beamworld/iWatch-Bilibili-TV-cover/output/render/iWatch_Bilibili-TV_AD.8.png

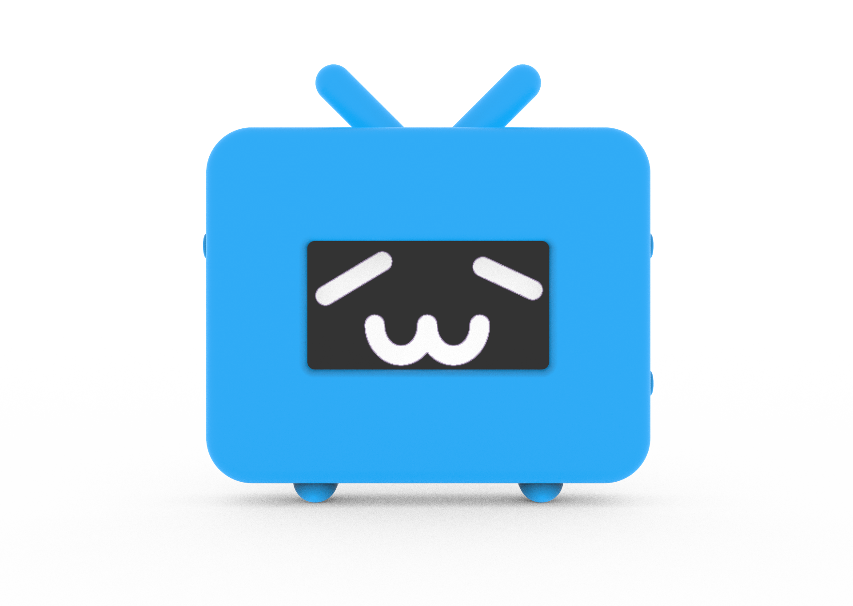
output/render/iWatch_Bilibili-TV_AD.8.png
