beamworld/iWatch-Bilibili-TV-cover/output/render/iWatch_Thin_cover_AD.8.jpg

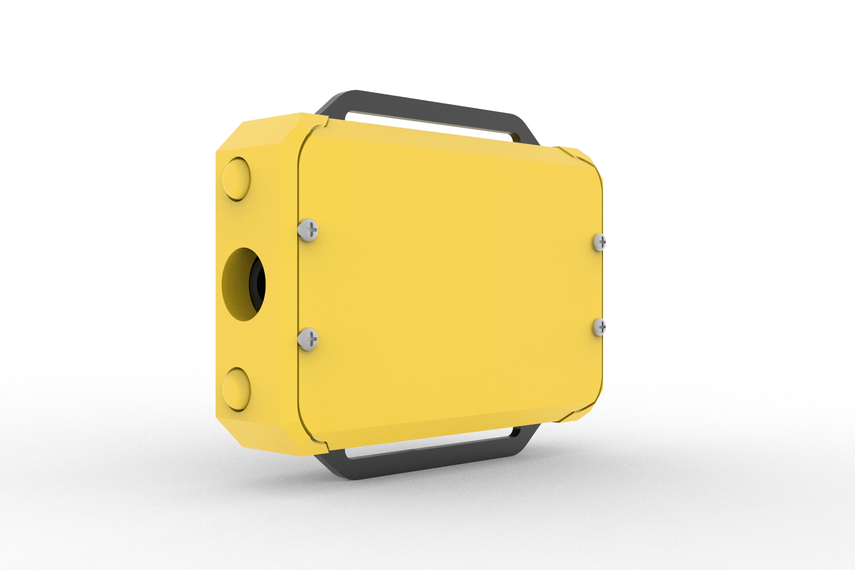
output/render/iWatch_Thin_cover_AD.8.jpg
