beamworld/iWatch-Bilibili-TV-cover/output/render/iWatch_unit_Rev0.9.png

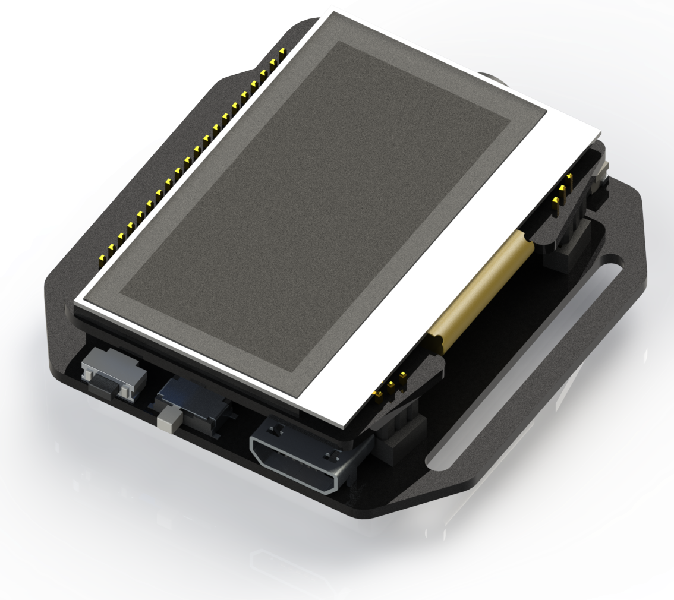
output/render/iWatch_unit_Rev0.9.png
