beamworld/iWatch-Bilibili-TV-cover/component/Beep/Beep_5020_SMT.SLDPRT

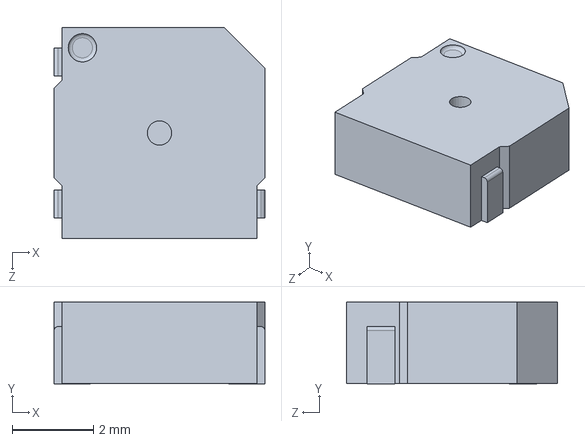
[picture p43: CAD file, 2020-08-19]
component/Beep/Beep_5020_SMT.SLDPRT
5.20 x 2.01 x 5.20 mm
