beamworld/iWatch-Bilibili-TV-cover/component/Button/Button_2x4mm_Side_SMT.SLDPRT

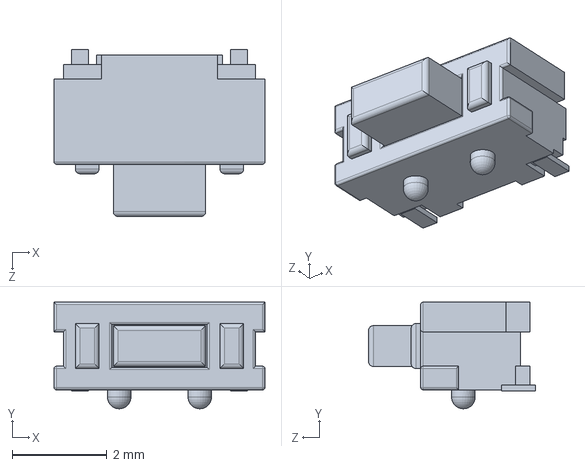
[picture p44: CAD file, 2020-08-19]
component/Button/Button_2x4mm_Side_SMT.SLDPRT
4.45 x 2.25 x 3.52 mm
