beamworld/iWatch-Bilibili-TV-cover/component/Header/Female-header_1.27mm_single_2mm-high.SLDPRT

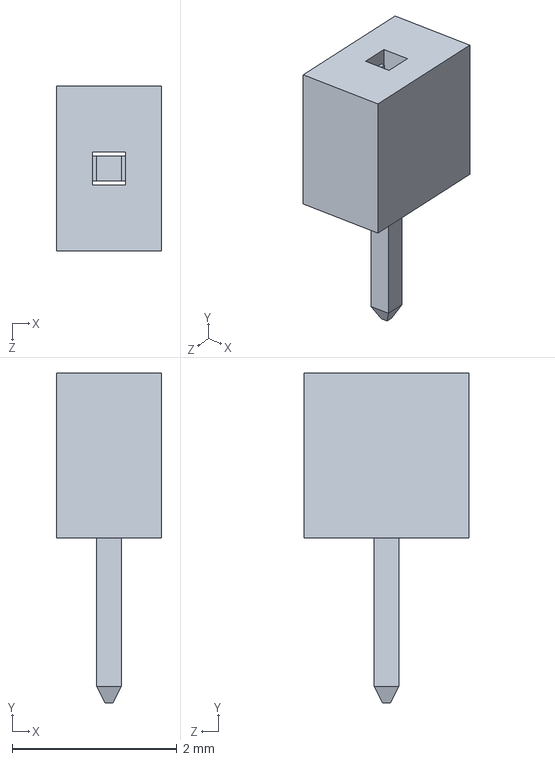
[picture p45: CAD file, 2020-08-19]
component/Header/Female-header_1.27mm_single_2mm-high.SLDPRT
1.27 x 4.00 x 2.00 mm
