beamworld/iWatch-Bilibili-TV-cover/component/IC/SOT23-6/SOT23-6.sldprt

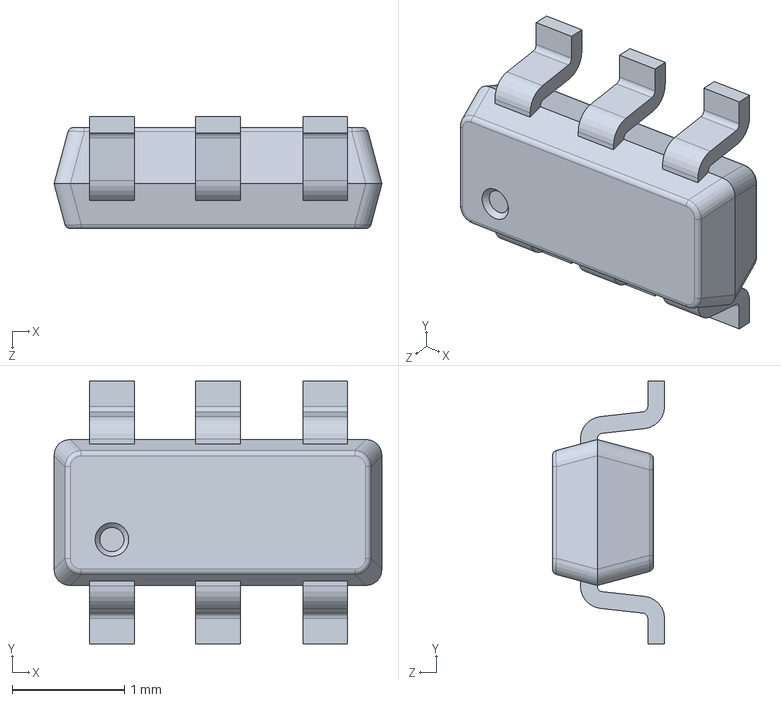
[picture p46: CAD file, 2020-08-19]
component/IC/SOT23-6/SOT23-6.sldprt
2.92 x 2.34 x 1.00 mm
