beamworld/iWatch-Bilibili-TV-cover/component/IC/STC51/STC51.SLDPRT

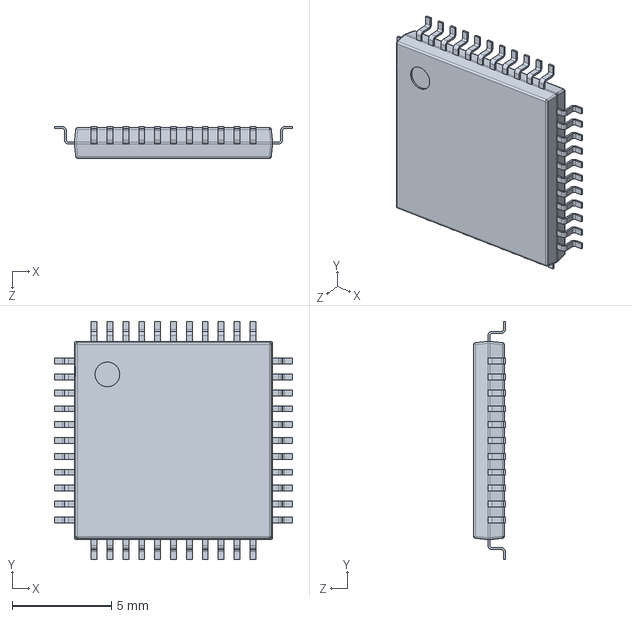
[picture p47: CAD file, 2020-08-19]
component/IC/STC51/STC51.SLDPRT
12.0 x 12.0 x 1.60 mm
