beamworld/iWatch-Bilibili-TV-cover/component/Jack/Phone_jack_PJ327A_5P_SMT.SLDPRT

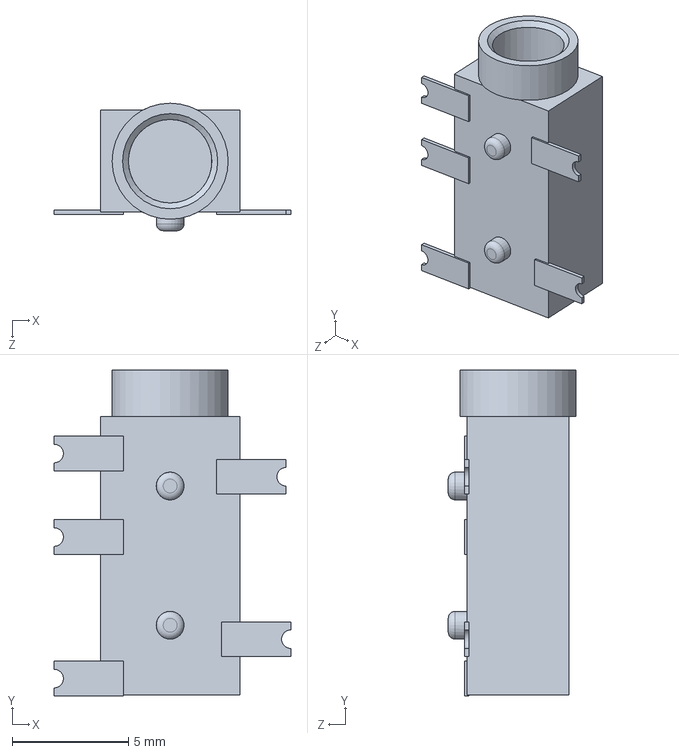
[picture p48: CAD file, 2020-08-19]
component/Jack/Phone_jack_PJ327A_5P_SMT.SLDPRT
10.2 x 14.1 x 5.50 mm
