beamworld/iWatch-Bilibili-TV-cover/component/OLED/1.3inch_OLED.sldprt

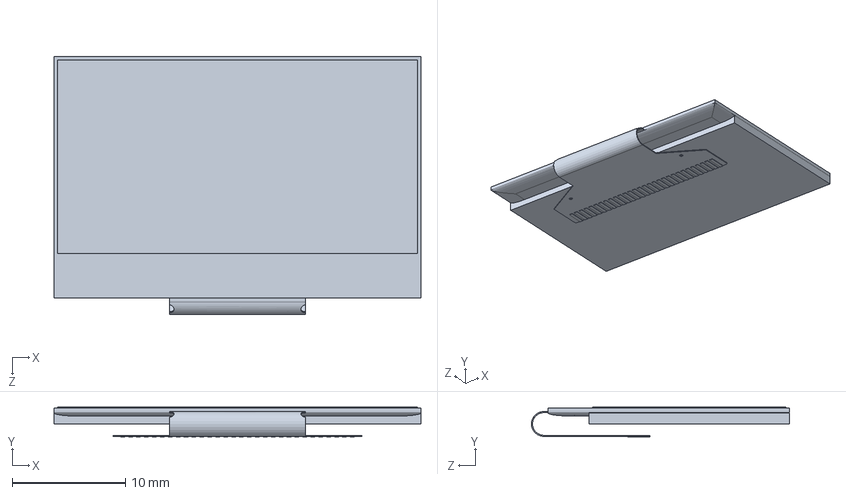
[picture p49: CAD file, 2020-08-19]
component/OLED/1.3inch_OLED.sldprt
32.4 x 2.65 x 22.8 mm
