beamworld/iWatch-Bilibili-TV-cover/component/Switch/Switch_mini_5x3mm_SPDT_Side_SMT.SLDPRT

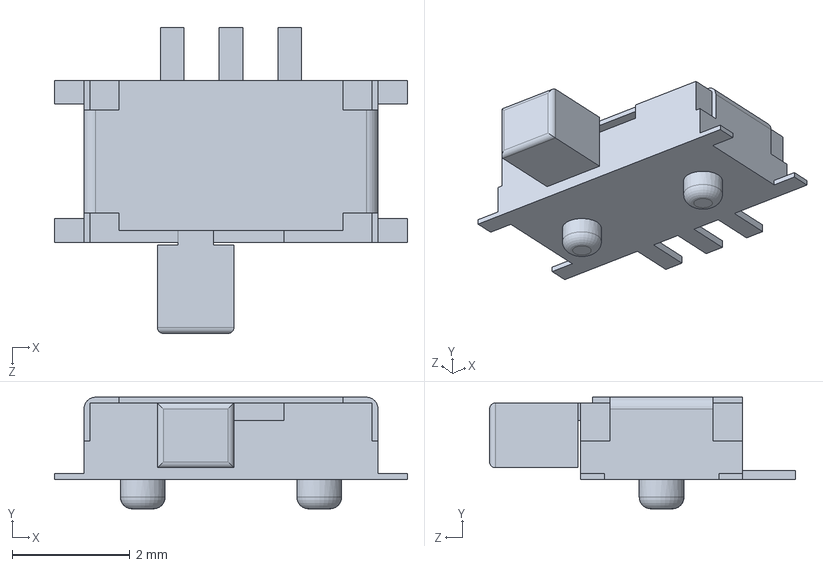
[picture p50: CAD file, 2020-08-19]
component/Switch/Switch_mini_5x3mm_SPDT_Side_SMT.SLDPRT
6.00 x 1.90 x 5.20 mm
