beamworld/iWatch-Bilibili-TV-cover/component/USB/MicroUSB_SMT.sldprt

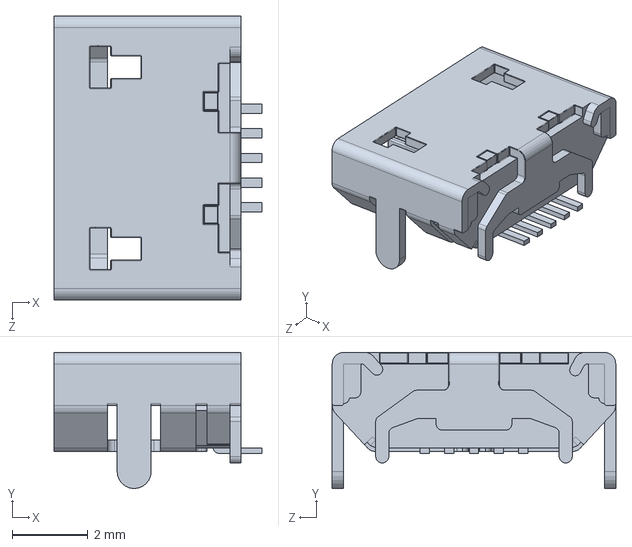
[picture p51: CAD file, 2020-08-19]
component/USB/MicroUSB_SMT.sldprt
5.50 x 3.60 x 7.50 mm
