beamworld/iWatch-Bilibili-TV-cover/output/stl/Bilibili_part1.STL

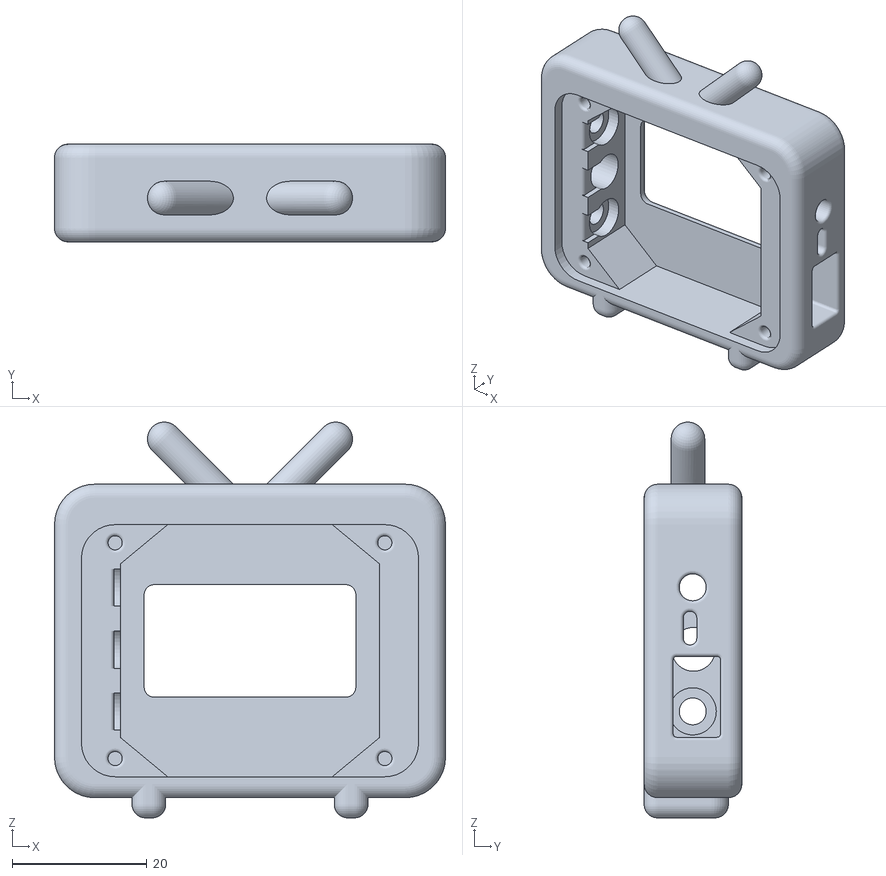
[picture p52: CAD file, 2020-08-21]
output/stl/Bilibili_part1.STL
58.0 x 14.5 x 58.7
