beamworld/iWatch-Bilibili-TV-cover/source/step/iWatch-screen.step

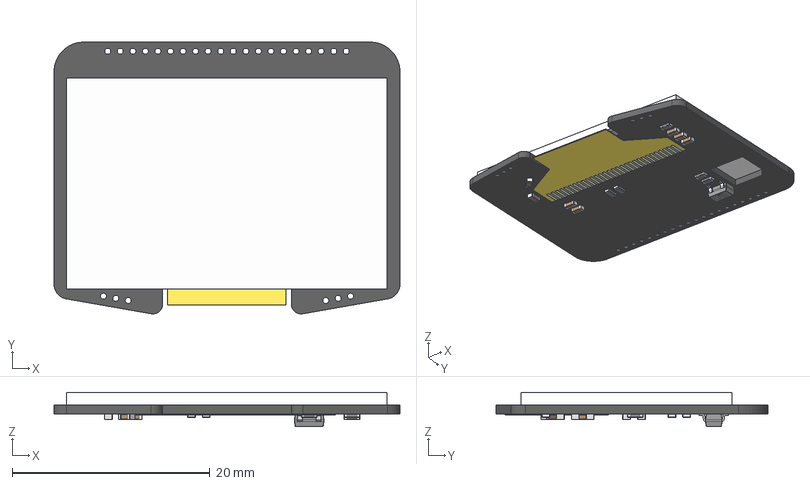
[picture p53: CAD file, 2020-08-19]
source/step/iWatch-screen.step
35.0 x 27.5 x 3.47 mm
Board
RESC1608(0603) x 5
SOT-23
CAPC1608(0603) x 7
Extruded x 35
