beamworld/iWatch-Bilibili-TV-cover/standard_part/M1.2x3.sldprt

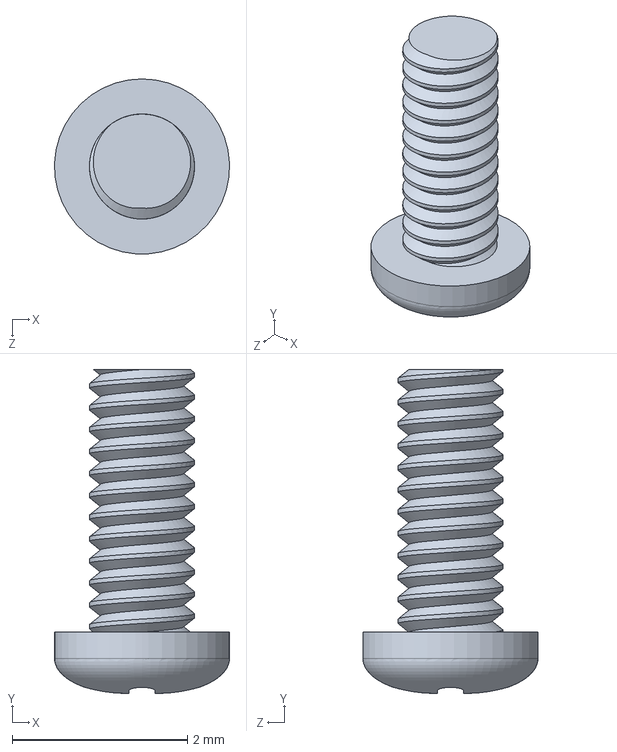
[picture p54: CAD file, 2020-08-20]
standard_part/M1.2x3.sldprt
2.00 x 3.70 x 2.00 mm
