beamworld/iWatch-Bilibili-TV-cover/component/0805/0805_R.sldprt

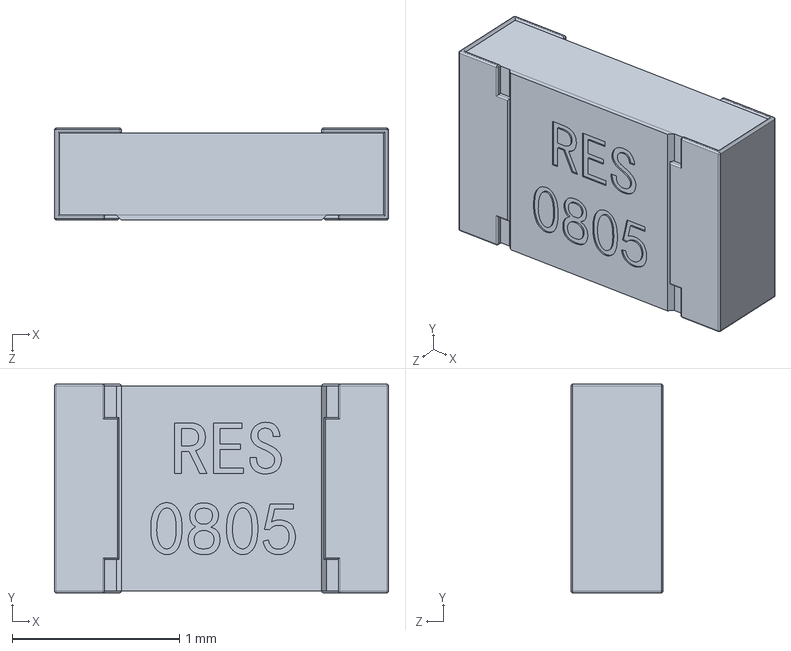
[picture p55: CAD file, 2020-08-19]
component/0805/0805_R.sldprt
2.00 x 1.25 x 0.55 mm
