beamworld/iWatch-Bilibili-TV-cover/component/Battery/Battery_protection_board.SLDPRT

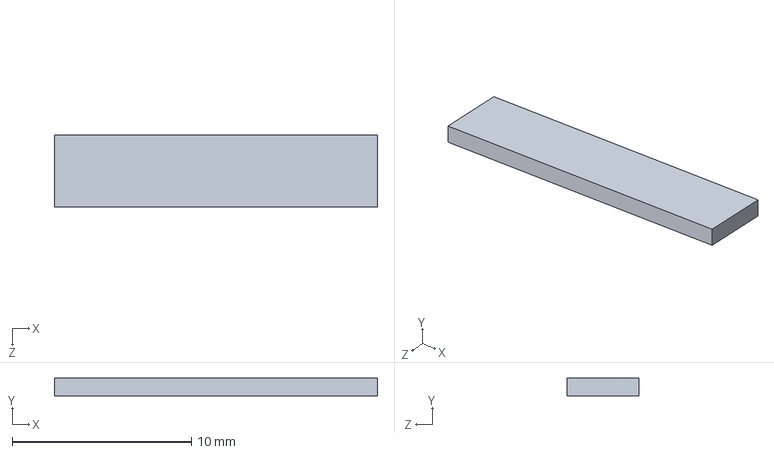
[picture p56: CAD file, 2020-08-19]
component/Battery/Battery_protection_board.SLDPRT
18.0 x 1.00 x 4.00 mm
