beamworld/iWatch-Bilibili-TV-cover/output/stl/Thin_cover_part1.STL

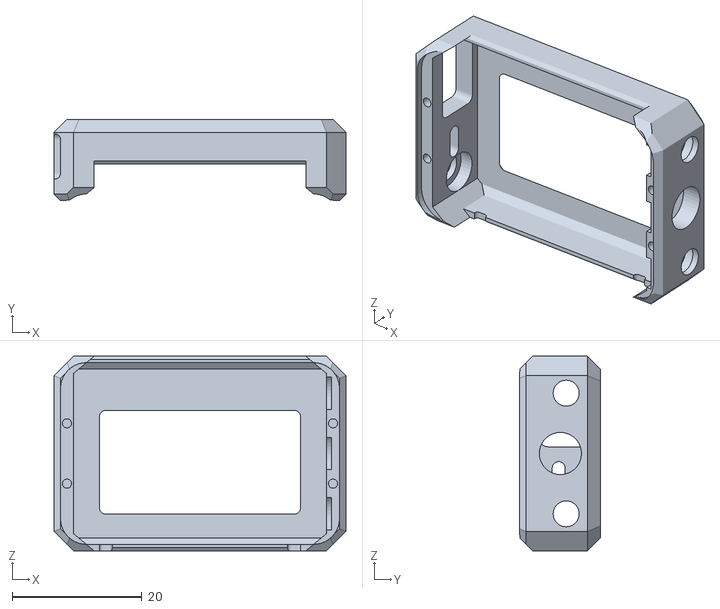
[picture p57: CAD file, 2020-08-21]
output/stl/Thin_cover_part1.STL
45.0 x 12.5 x 30.0
