beamworld/iWatch-Bilibili-TV-cover/component/0805/0805_LED.sldprt

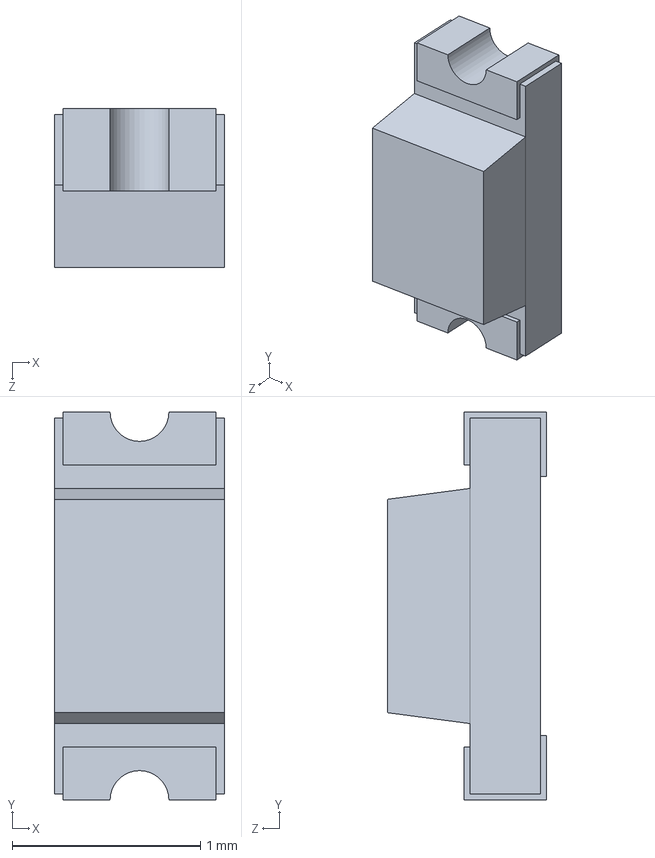
[picture p58: CAD file, 2020-08-19]
component/0805/0805_LED.sldprt
0.906 x 2.06 x 0.844 mm
