beamworld/iWatch-Bilibili-TV-cover/output/stl/Thin_cover_part2_cap.STL

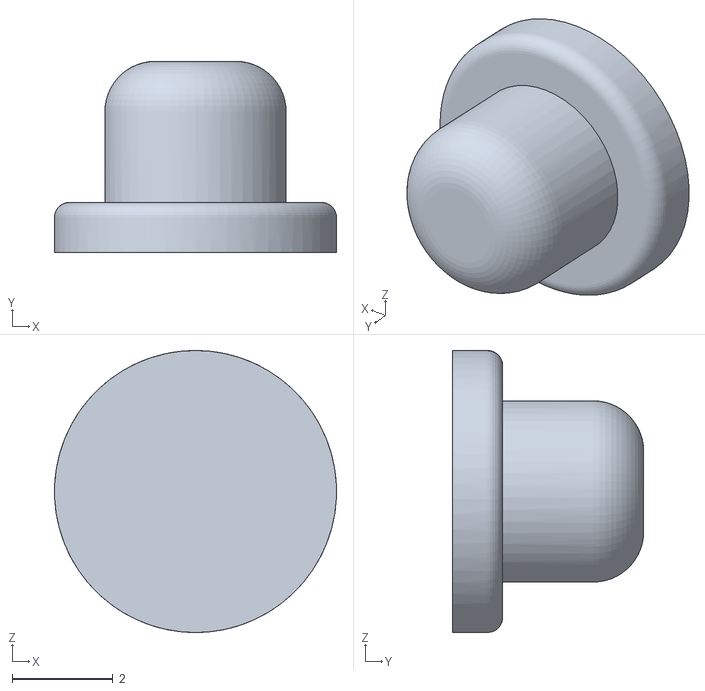
[picture p59: CAD file, 2020-08-21]
output/stl/Thin_cover_part2_cap.STL
5.60 x 3.80 x 5.60
