beamworld/iWatch-Bilibili-TV-cover/output/stl/Thin_cover_part3.STL

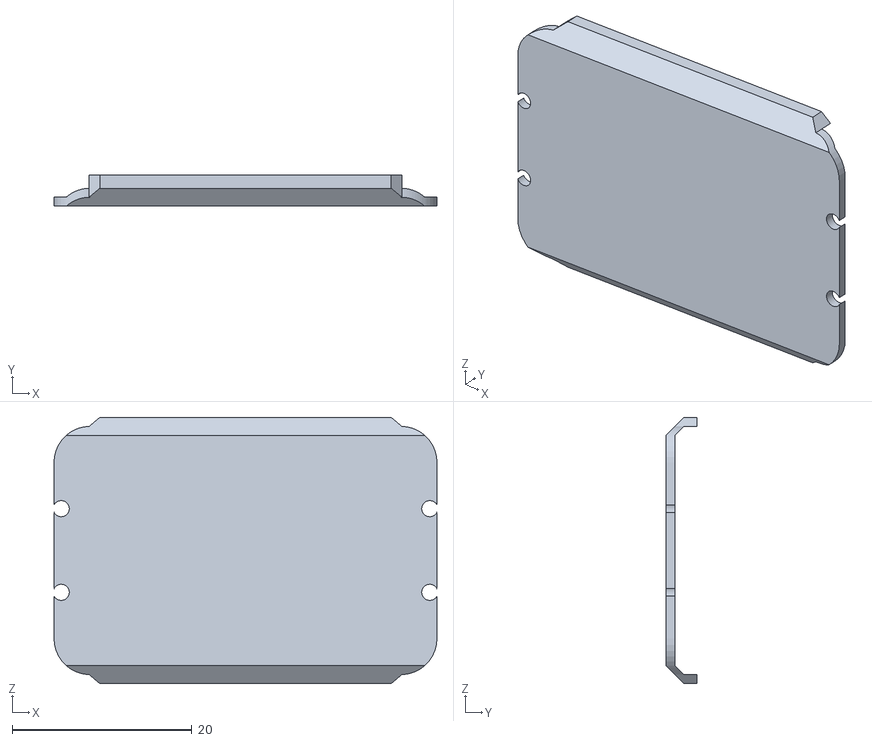
[picture p60: CAD file, 2020-08-20]
output/stl/Thin_cover_part3.STL
42.6 x 3.50 x 29.6
