beamworld/iWatch-Bilibili-TV-cover/component/Battery/0402_R.sldprt

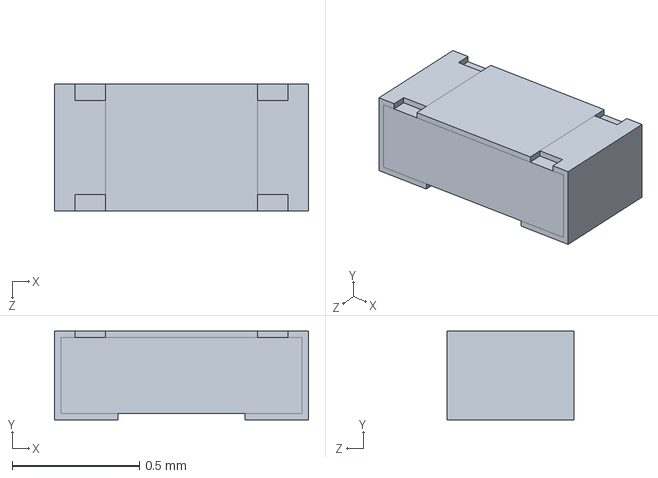
[picture p61: CAD file, 2020-08-19]
component/Battery/0402_R.sldprt
1.00 x 0.35 x 0.5 mm
