beamworld/iWatch-Bilibili-TV-cover/output/stl/Bilibili_part3.STL

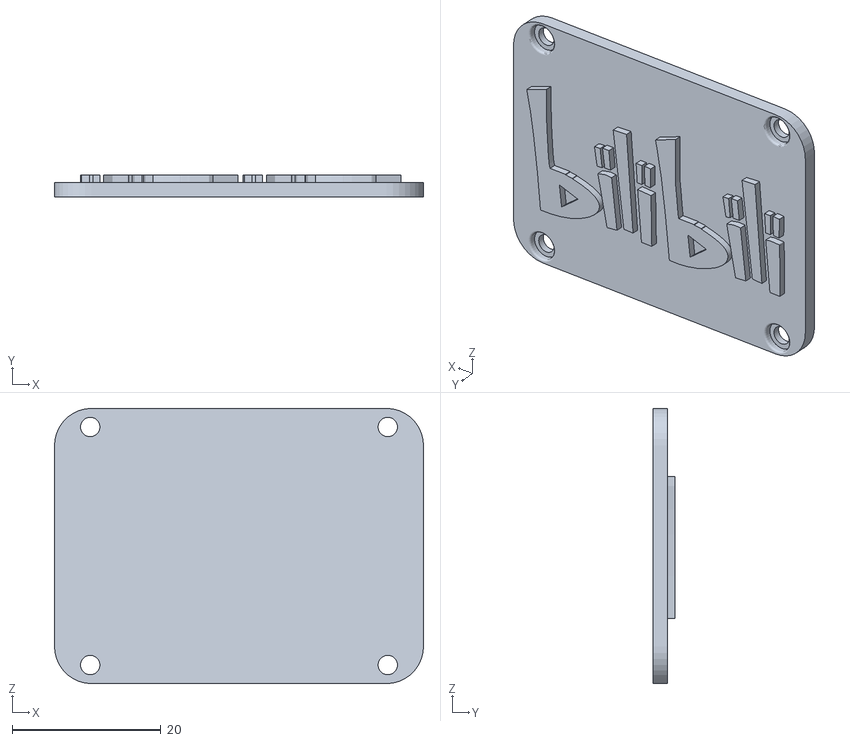
[picture p62: CAD file, 2020-08-20]
output/stl/Bilibili_part3.STL
49.6 x 3.00 x 37.0
