beamworld/iWatch-Bilibili-TV-cover/component/Battery/0201_R.SLDPRT

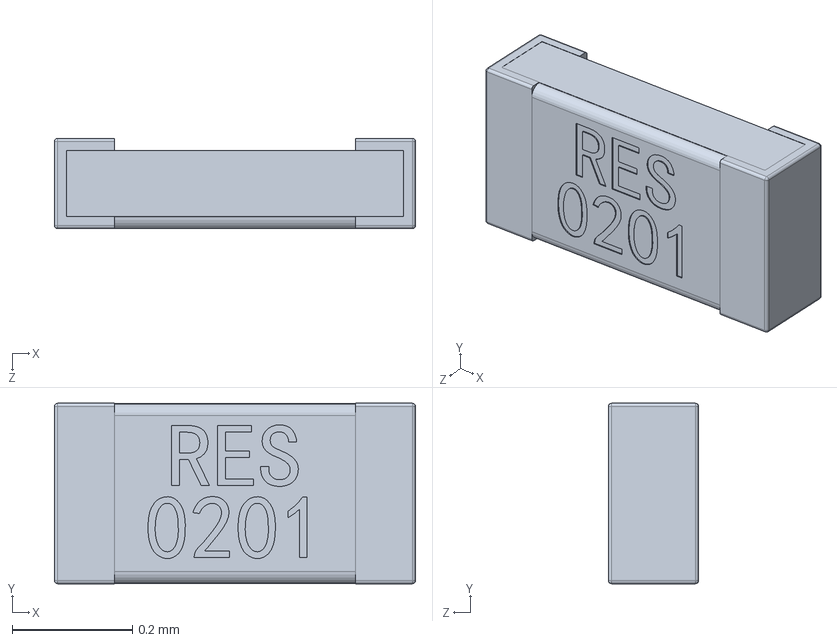
[picture p63: CAD file, 2020-08-19]
component/Battery/0201_R.SLDPRT
0.6 x 0.3 x 0.15 mm
