beamworld/iWatch-Bilibili-TV-cover/component/Header/Male-header_1.27mm_single_2mm-high.SLDPRT

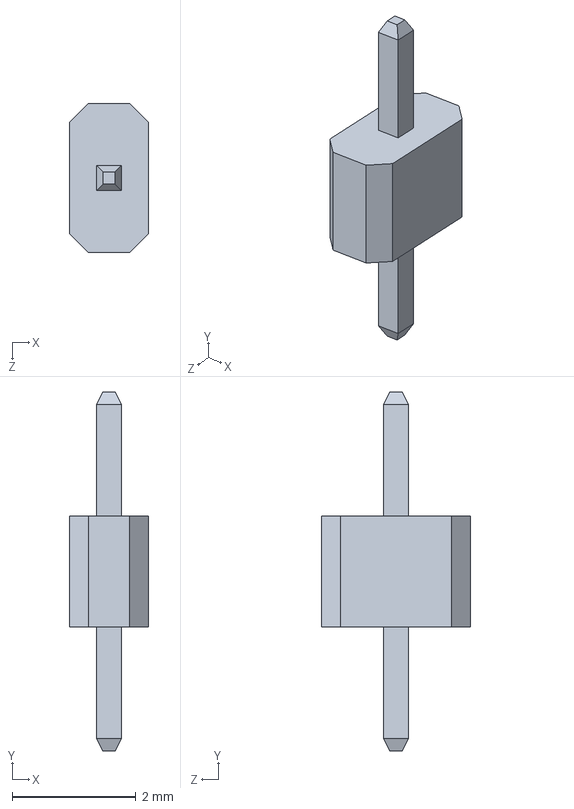
[picture p64: CAD file, 2020-08-19]
component/Header/Male-header_1.27mm_single_2mm-high.SLDPRT
1.27 x 5.80 x 2.40 mm
