beamworld/iWatch-Bilibili-TV-cover/output/stl/Bilibili_part2_cap.STL

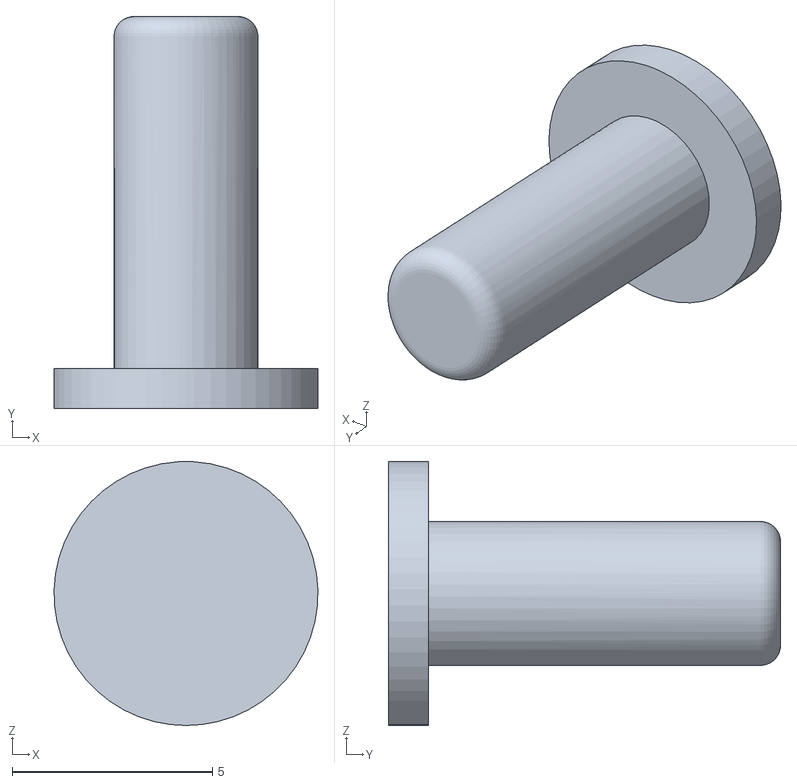
[picture p65: CAD file, 2020-08-19]
output/stl/Bilibili_part2_cap.STL
6.60 x 9.80 x 6.60
