beamworld/iWatch-Bilibili-TV-cover/special_part/top_board.SLDPRT

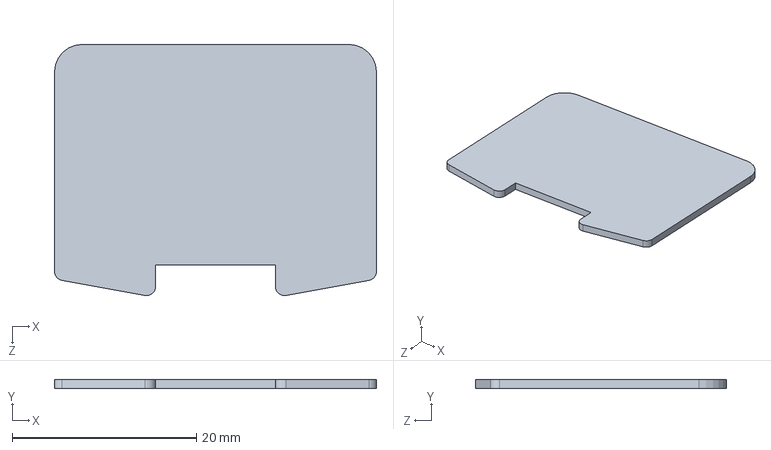
[picture p66: CAD file, 2020-08-19]
special_part/top_board.SLDPRT
35.0 x 1.00 x 27.3 mm
