beamworld/iWatch-Bilibili-TV-cover/component/Battery/Battery_31x25mm_200mAh_3.7V_Li_cell.SLDPRT

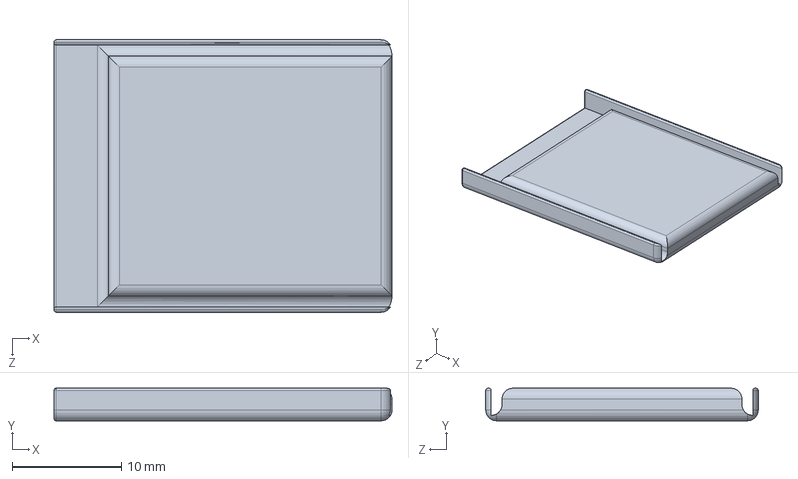
[picture p67: CAD file, 2020-08-19]
component/Battery/Battery_31x25mm_200mAh_3.7V_Li_cell.SLDPRT
31.0 x 3.00 x 25.0 mm
