beamworld/iWatch-Bilibili-TV-cover/special_part/bottom_board.SLDPRT

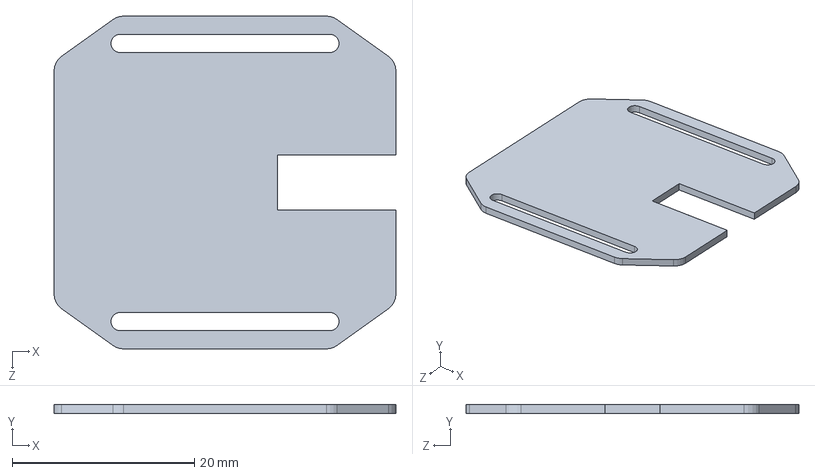
[picture p68: CAD file, 2020-08-19]
special_part/bottom_board.SLDPRT
37.5 x 1.00 x 36.5 mm
